flyinglightspeck/FLS/LightBenderv11/3d/rod_link_2x.3mf

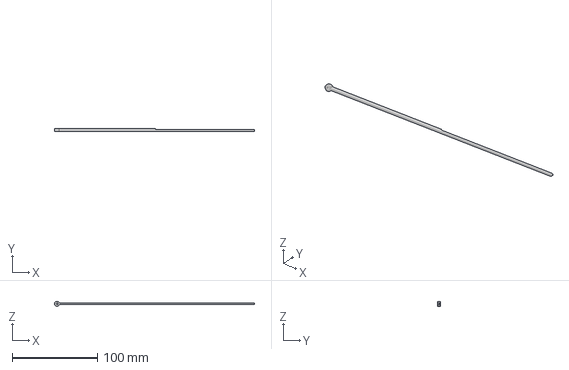
[picture p38: CAD file, 2026-01-12]
LightBenderv11/3d/rod_link_2x.3mf
234.0 x 3.00 x 5.50 mm
