flyinglightspeck/FLS/LightBenderv11/3d/shaft_holder_2_nb-3002.3mf

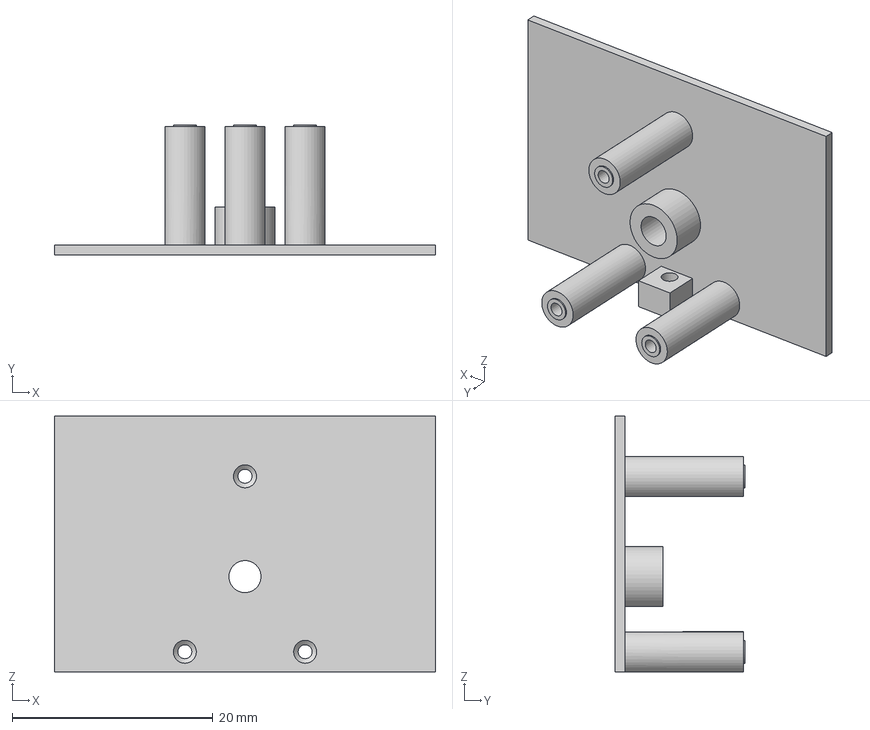
[picture p39: CAD file, 2026-01-12]
LightBenderv11/3d/shaft_holder_2_nb-3002.3mf
38.0 x 12.9 x 25.5 mm
