flyinglightspeck/FLS/LightBenderv11/3d/tube_fin.3mf

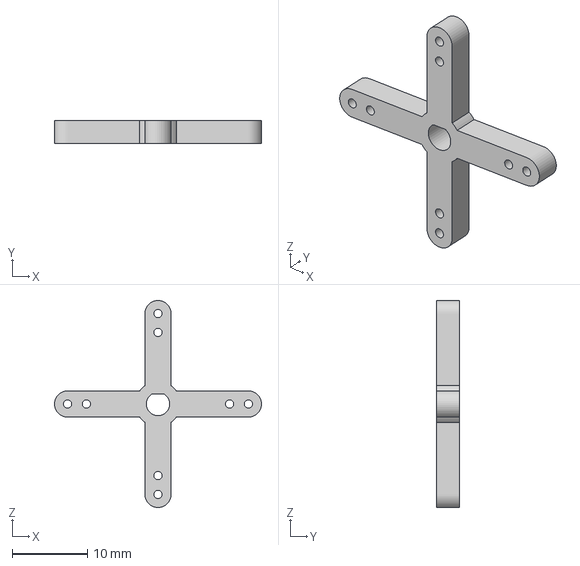
[picture p40: CAD file, 2026-01-12]
LightBenderv11/3d/tube_fin.3mf
27.6 x 3.00 x 27.6 mm
