flyinglightspeck/FLS/LightBenderv11/3d/servo_holder_nb-3002.3mf

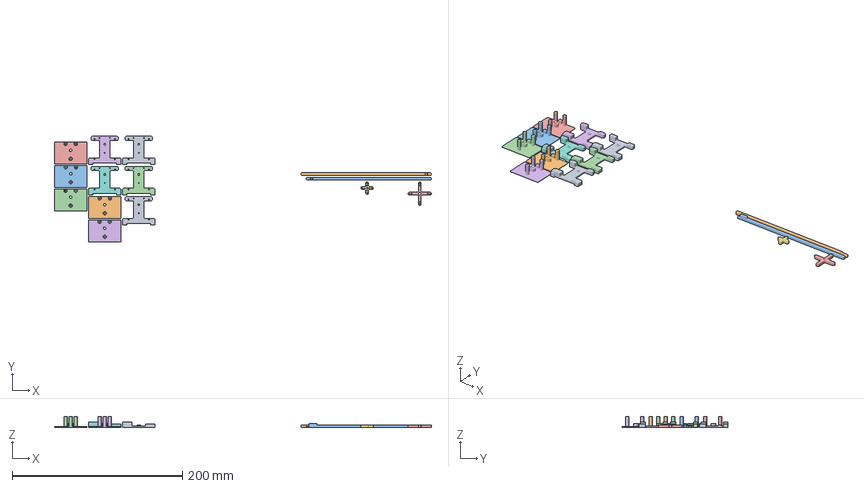
[picture p41: CAD file, 2026-01-12]
LightBenderv11/3d/servo_holder_nb-3002.3mf
442.9 x 124.0 x 12.9 mm
servo_holder x 5
rof_link_fin
tube_link_fin
tube_fin
rod_fin
shaft_holder_2 x 5
