flyinglightspeck/FLS/LightBenderv11/3d/tube_fin_m1.2.3mf

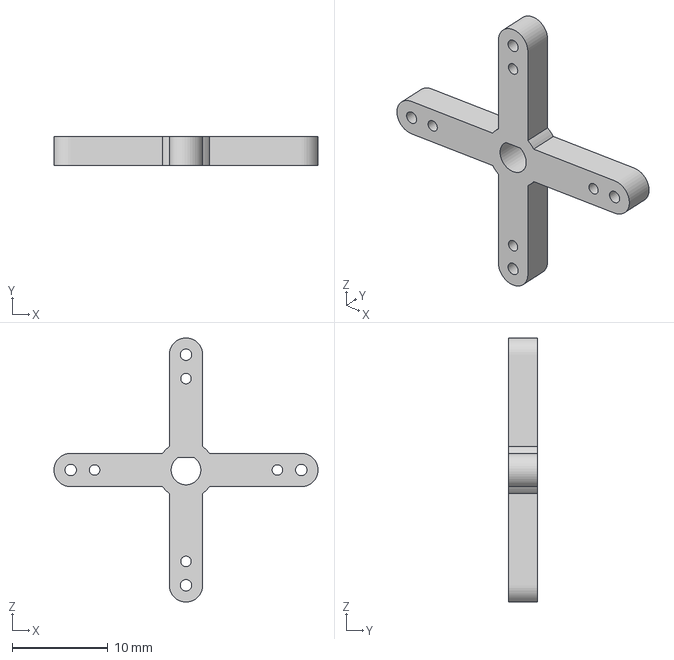
[picture p42: CAD file, 2026-01-12]
LightBenderv11/3d/tube_fin_m1.2.3mf
27.6 x 3.00 x 27.6 mm
