flyinglightspeck/FLS/LightBenderv11/3d/tube_link_2_170mm.3mf

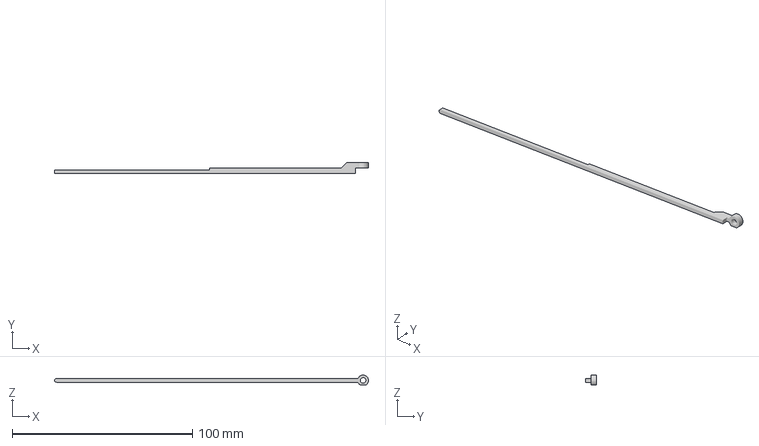
[picture p43: CAD file, 2026-01-12]
LightBenderv11/3d/tube_link_2_170mm.3mf
174.0 x 6.00 x 5.50 mm
