flyinglightspeck/FLS/LightBenderv11/3d/tube_link_2x.3mf

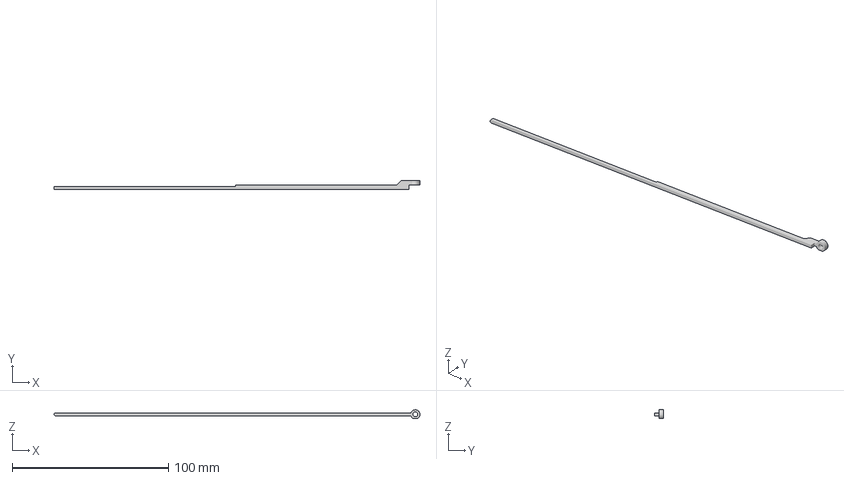
[picture p44: CAD file, 2026-01-12]
LightBenderv11/3d/tube_link_2x.3mf
234.0 x 6.00 x 5.50 mm
