flyinglightspeck/FLS/LightBenderv11/3d/rod_link_d.3mf

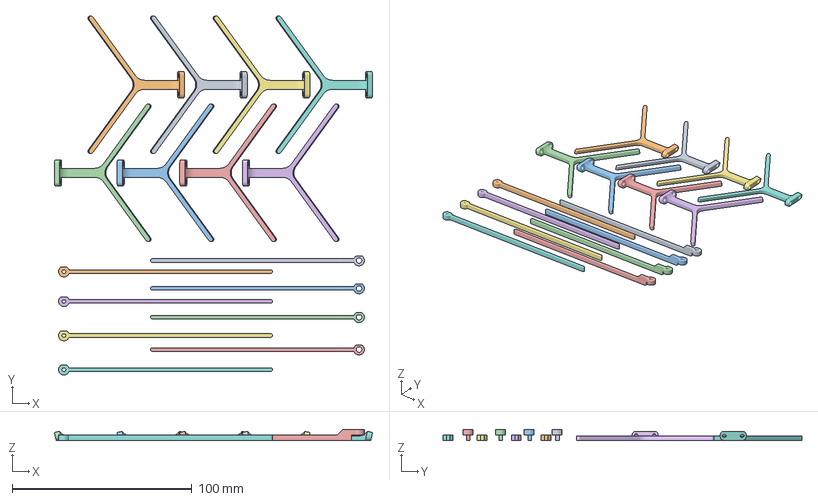
[picture p45: CAD file, 2026-01-12]
LightBenderv11/3d/rod_link_d.3mf
177.0 x 199.6 x 6.00 mm
tube_link_2 x 4
rod_link x 4
landing_gear x 8
