flyinglightspeck/FLS/LightBenderv11/3d/rod_fin_2.3mf

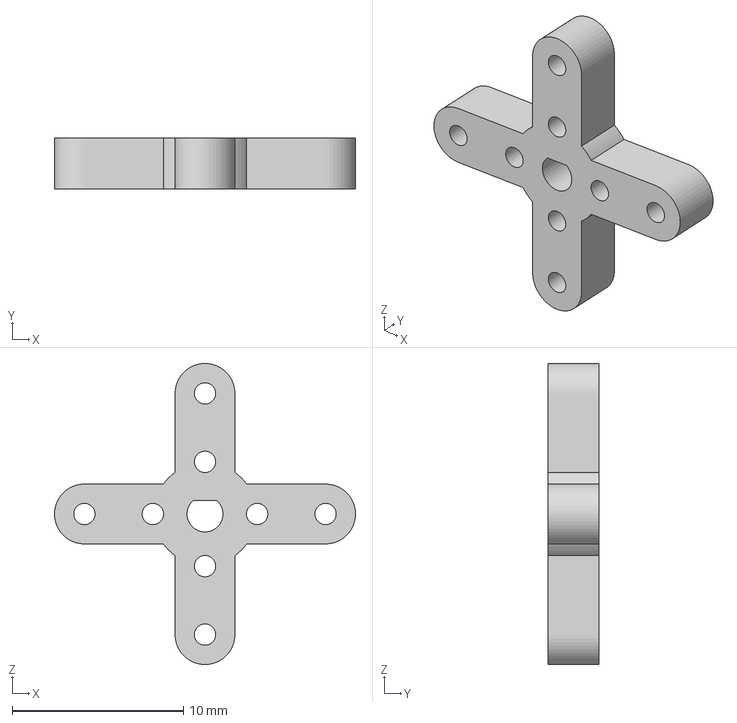
[picture p46: CAD file, 2026-01-12]
LightBenderv11/3d/rod_fin_2.3mf
17.6 x 3.00 x 17.6 mm
