flyinglightspeck/FLS/LightBenderv11/3d/servo_holder.3mf

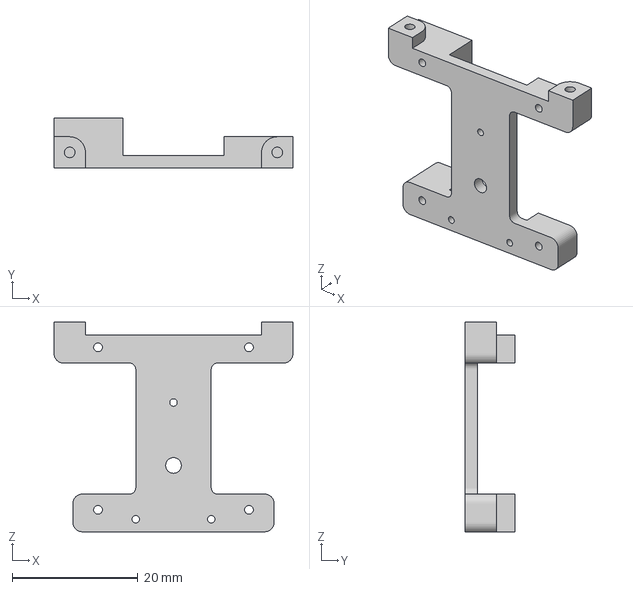
[picture p47: CAD file, 2026-01-12]
LightBenderv11/3d/servo_holder.3mf
38.0 x 8.00 x 33.3 mm
