flyinglightspeck/FLS/LightBenderv11/3d/rod_fin_m1.2.3mf

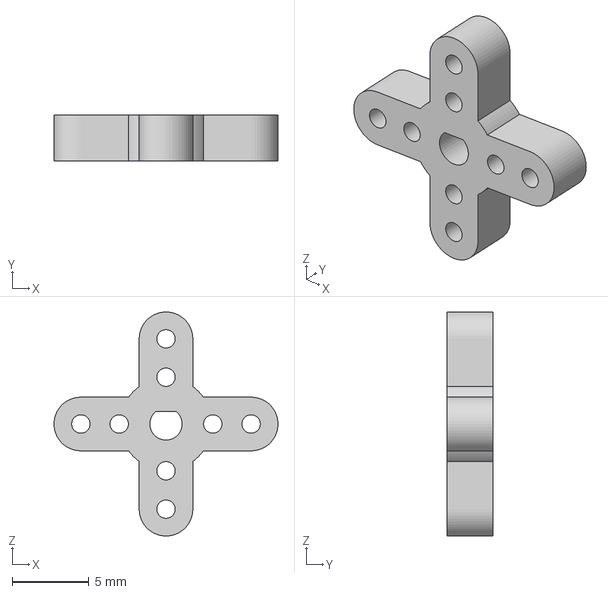
[picture p48: CAD file, 2026-01-12]
LightBenderv11/3d/rod_fin_m1.2.3mf
14.6 x 3.00 x 14.6 mm
