flyinglightspeck/FLS/LightBenderv11/3d/shaft_holder.3mf

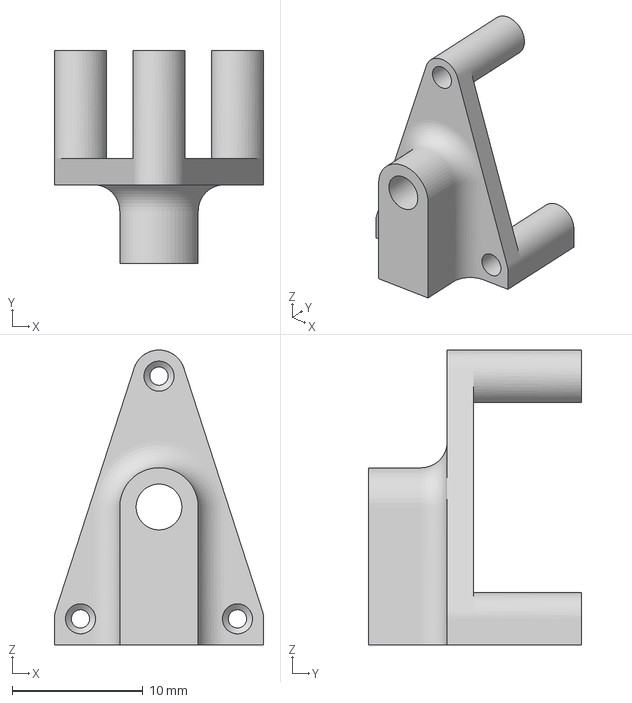
[picture p49: CAD file, 2026-01-12]
LightBenderv11/3d/shaft_holder.3mf
16.0 x 16.2 x 22.6 mm
