flyinglightspeck/FLS/LightBenderv11/3d/rof_link_fin.3mf

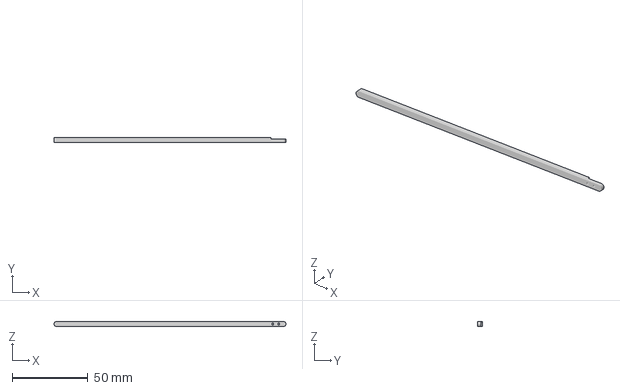
[picture p50: CAD file, 2026-01-12]
LightBenderv11/3d/rof_link_fin.3mf
153.5 x 3.00 x 3.50 mm
